zapta/power-monitors/pmon_5v/eagle/pmon_5v_board.pdf

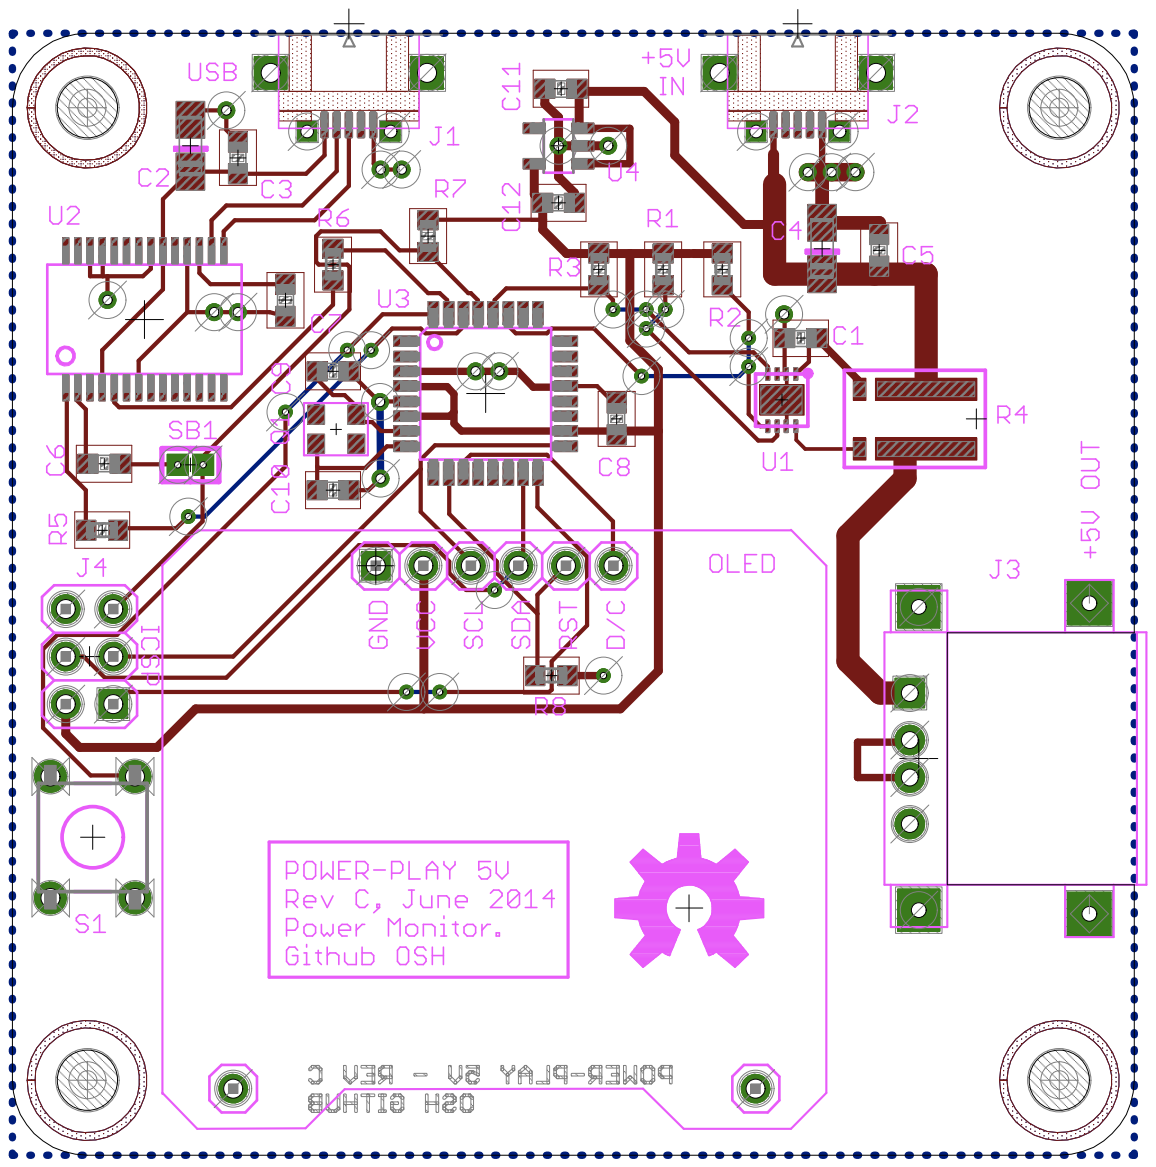
[picture p16: page 1]
