zapta/power-monitors/pmon_uno/eagle/powermon.brd

## EAGLE design pmon_uno/eagle/powermon.brd (2014-04-19)

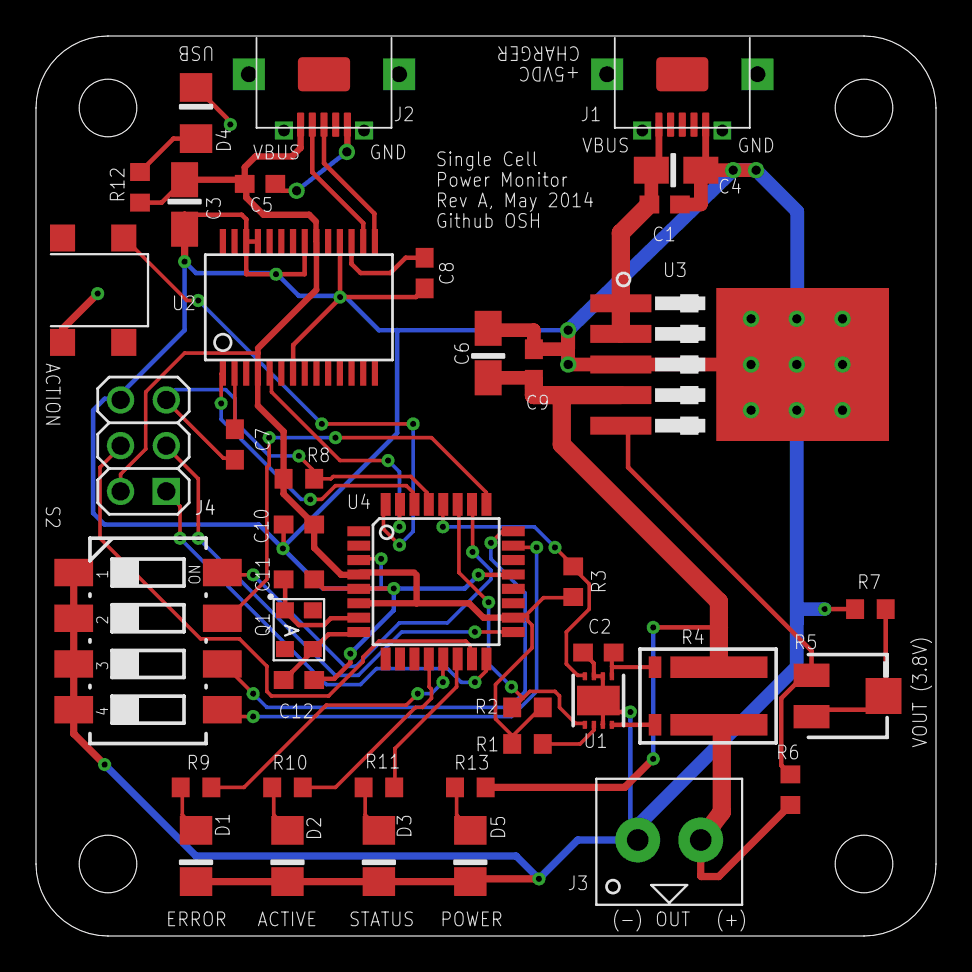
[picture p25: board powermon.brd from above]

Board: 2 copper layers, 50.0 x 50.0 mm, 42 parts (0 on the bottom side), 37 nets.

Parts:
C1, C3, C6: 10uF; A/3216-18R
C2: 1uF; C0603
C4, C5, C7, C8, C9, C10: 0.1uF; C0603
C11, C12: 20pF; C0603
D1: RED; 1206-LED
D2, D3: GREEN; 1206-LED
D4, D5: BLUE; 1206-LED
J1, J2: USB; USB-MICRO-ZX62RD-AB-5P8
J3: TERMINAL-2
J4: 2X03
PCB1: PCB_DP_SQUARE-5X5; DP5050_V1
Q1: CRYSTAL-CTS406
R1, R8: 10K; R0603
R2, R3: 4.7K; R0603
R4: 0.025R 1%; SHUNT
R5: 1K; TRIM-POT_SM-42/43A
R6: 8K2 1%; R0603
R7: 3.3K 1%; R0603
R9, R10, R11, R12, R13: 3.3K; R0603
S1: PUSH_BUTTONEVQPSL; EVQPSL-PUSH-BUTTON
S2: 219-04; CTS-219-04
U1: LTC2943; DFN8-3X3
U2: FT232RL; SSOP28DB
U3: LT1764AEQ; TO263-5
U4: ATMEGA328TQFP32; TQFP32-08

Connections:
+5V: C3.+, C5.1, C10.1, J2.1, J4.2, R1.2, R2.2, R3.2, R8.2, R12.1, U2.4, U2.20, U4.4, U4.6, U4.18
ACTION: S1.1, U4.32
ACTIVITY_LED: R10.2, U4.12
CONFIG1: S2.8, U4.26
CONFIG2: S2.7, U4.25
CONFIG3: S2.6, U4.24
CONFIG4: S2.5, U4.23
DEBUG_LED: R11.2, U4.14
ERROR_LED: R9.2, U4.13
GND: C1.-, C2.2, C3.-, C4.2, C5.2, C6.-, C8.2, C9.2, C10.2, C11.2, C12.2, D1.C, D2.C, D3.C, D4.C, D5.C, J1.5, J2.5, J3.1, J4.6, R7.2, S1.2, S2.1, S2.2, S2.3, S2.4, U1.2, U1.3, U1.7, U1.EXP, U2.7, U2.18, U2.21, U2.25, U2.26, U3.3, U3.6, U4.3, U4.5, U4.21
I2C-CLK: R3.1, U1.4, U4.28
I2C-DATA: R2.1, U1.5, U4.27
MISO: J4.1, U4.16
MOSI: J4.4, U4.15
unnamed: R1.1, U1.6
unnamed: C11.1, Q1.1, U4.7
unnamed: D2.A, R10.1
unnamed: D1.A, R9.1
unnamed: C12.1, Q1.3, U4.8
unnamed: C1.+, C4.1, J1.1, U3.1, U3.2
unnamed: J2.3, U2.15
unnamed: C7.1, U2.2
unnamed: D5.A, R13.2
unnamed: J2.2, U2.16
unnamed: C8.1, U2.17
unnamed: D4.A, R12.2
unnamed: R5.1, R5.2, R7.1
unnamed: R5.3, R6.2, U3.5
unnamed: D3.A, R11.1
unnamed: J3.2, R4.I1, R6.1
RESET: C7.2, J4.5, R8.1, U4.29
SCK: J4.3, U4.17
SENSE+: C2.1, R4.V2, U1.1
SENSE-: R4.V1, U1.8
SER_RX: U2.1, U4.30
SER_TX: U2.5, U4.31
V+: C6.+, C9.1, R4.I2, R13.1, U3.4
