zapta/power-monitors/pmon_3v8/arduino/byte_debouncer.h

// Licensed under the Apache License, Version 2.0 (the "License");
// you may not use this file except in compliance with the License.
// You may obtain a copy of the License at
//
//    http://www.apache.org/licenses/LICENSE-2.0
//
// Unless required by applicable law or agreed to in writing, software
// distributed under the License is distributed on an "AS IS" BASIS,
// WITHOUT WARRANTIES OR CONDITIONS OF ANY KIND, either express or implied.
// See the License for the specific language governing permissions and
// limitations under the License.

#ifndef BYTE_DEBOUNCER_H
#define BYTE_DEBOUNCER_H

#include "passive_timer.h"
#include <arduino.h>

// A class for debouncing 8 bits signal.
class ByteDebouncer {
private:
 public:
  ByteDebouncer(uint16 debounce_time_millis) 
   : 
    debounce_time_millis_(debounce_time_millis) {
      restart();
    }

  // Reset using a new debunce time. This resets hasStableValue() to false.
  void restart() {
    latest_value_ = 0x00;
    time_in_latest_value_.restart();
    has_stable_value_ = false;
    stable_value_ = 0x00;
  }

  // Update the debouncer state with a new input value.
  void update(uint8 new_value) {
    // Handle changes in latest value.
    if (new_value != latest_value_) {
      latest_value_ = new_value;
      time_in_latest_value_.restart();
      return;
    } 

    // If latest value is stable for debouncing time period, propagate value
    // to stable.
    if (time_in_latest_value_.timeMillis() > debounce_time_millis_) {
      has_stable_value_ = true;
      stable_value_ = latest_value_;
    }
  }

  // Test if the debouncer has a stable value. 
  boolean hasStableValue() const {
    return has_stable_value_;
  }

  // Returns the debounced state. Valid only if hasStableValue() is true.
  uint8 stableValue() const {
    return stable_value_;
  }

private:
  const uint16 debounce_time_millis_;

  // Tracks pre debouncing state.
  uint8 latest_value_;
  PassiveTimer time_in_latest_value_;

  // The debounced state.
  boolean has_stable_value_;
  uint8 stable_value_;
};

#endif
